s-light/lvds_4ch_link/driver/export/board_pdf/driver-F.SilkS.pdf

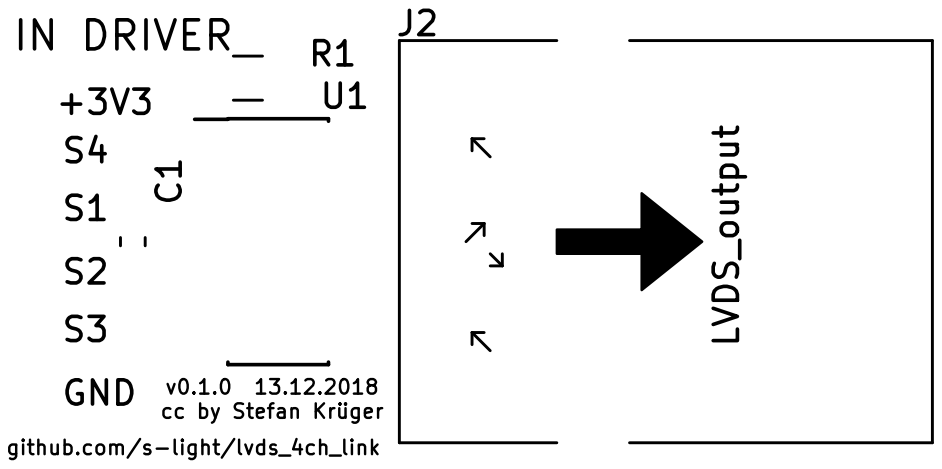
[picture p11: page 1]

cc by Stefan Krüger DRIVER
