s-light/lvds_4ch_link/receiver/export/board_pdf/receiver-B.Cu.pdf

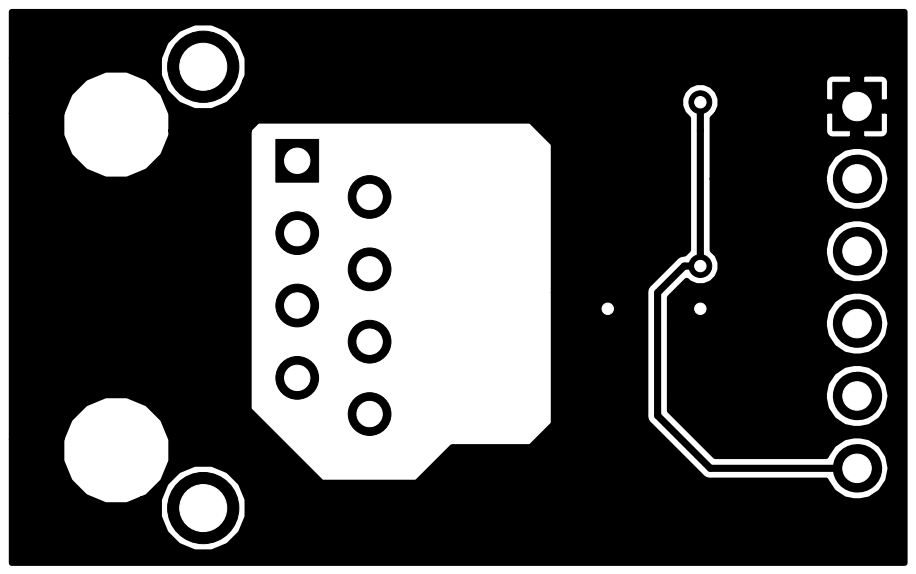
[picture p12: page 1]

Stefan Krüger CC BY Open Source Hardware

File: receiver.kicad_pcb Sheet: s-light.eu

Id: 1/1 Title: LVDS 4ch Driver
