s-light/lvds_4ch_link/receiver/export/board_pdf/receiver-F.SilkS.pdf

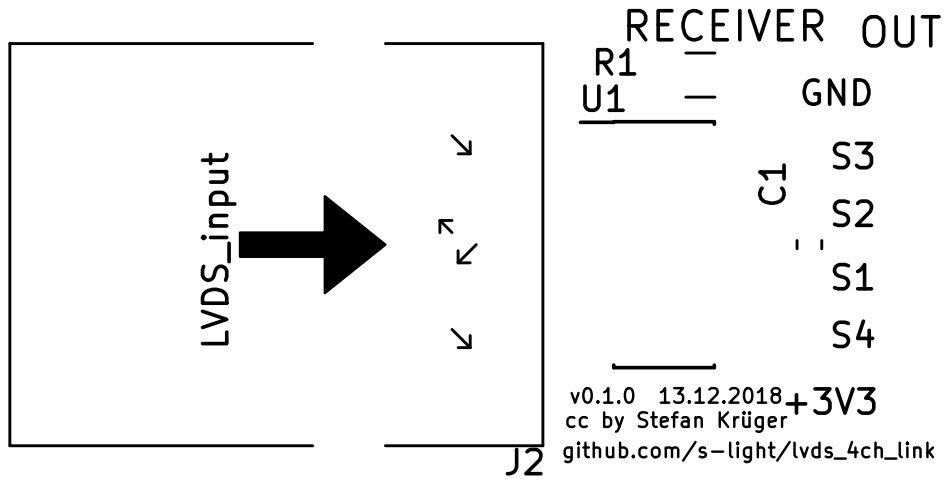
[picture p13: page 1]

cc by Stefan Krüger RECEIVER
S3S2S1 GND

Stefan Krüger CC BY Open Source Hardware

File: receiver.kicad_pcb Sheet: s-light.eu

Id: 1/1 Title: LVDS 4ch Driver
