s-light/lvds_4ch_link/driver/export/board_pdf/output.pdf

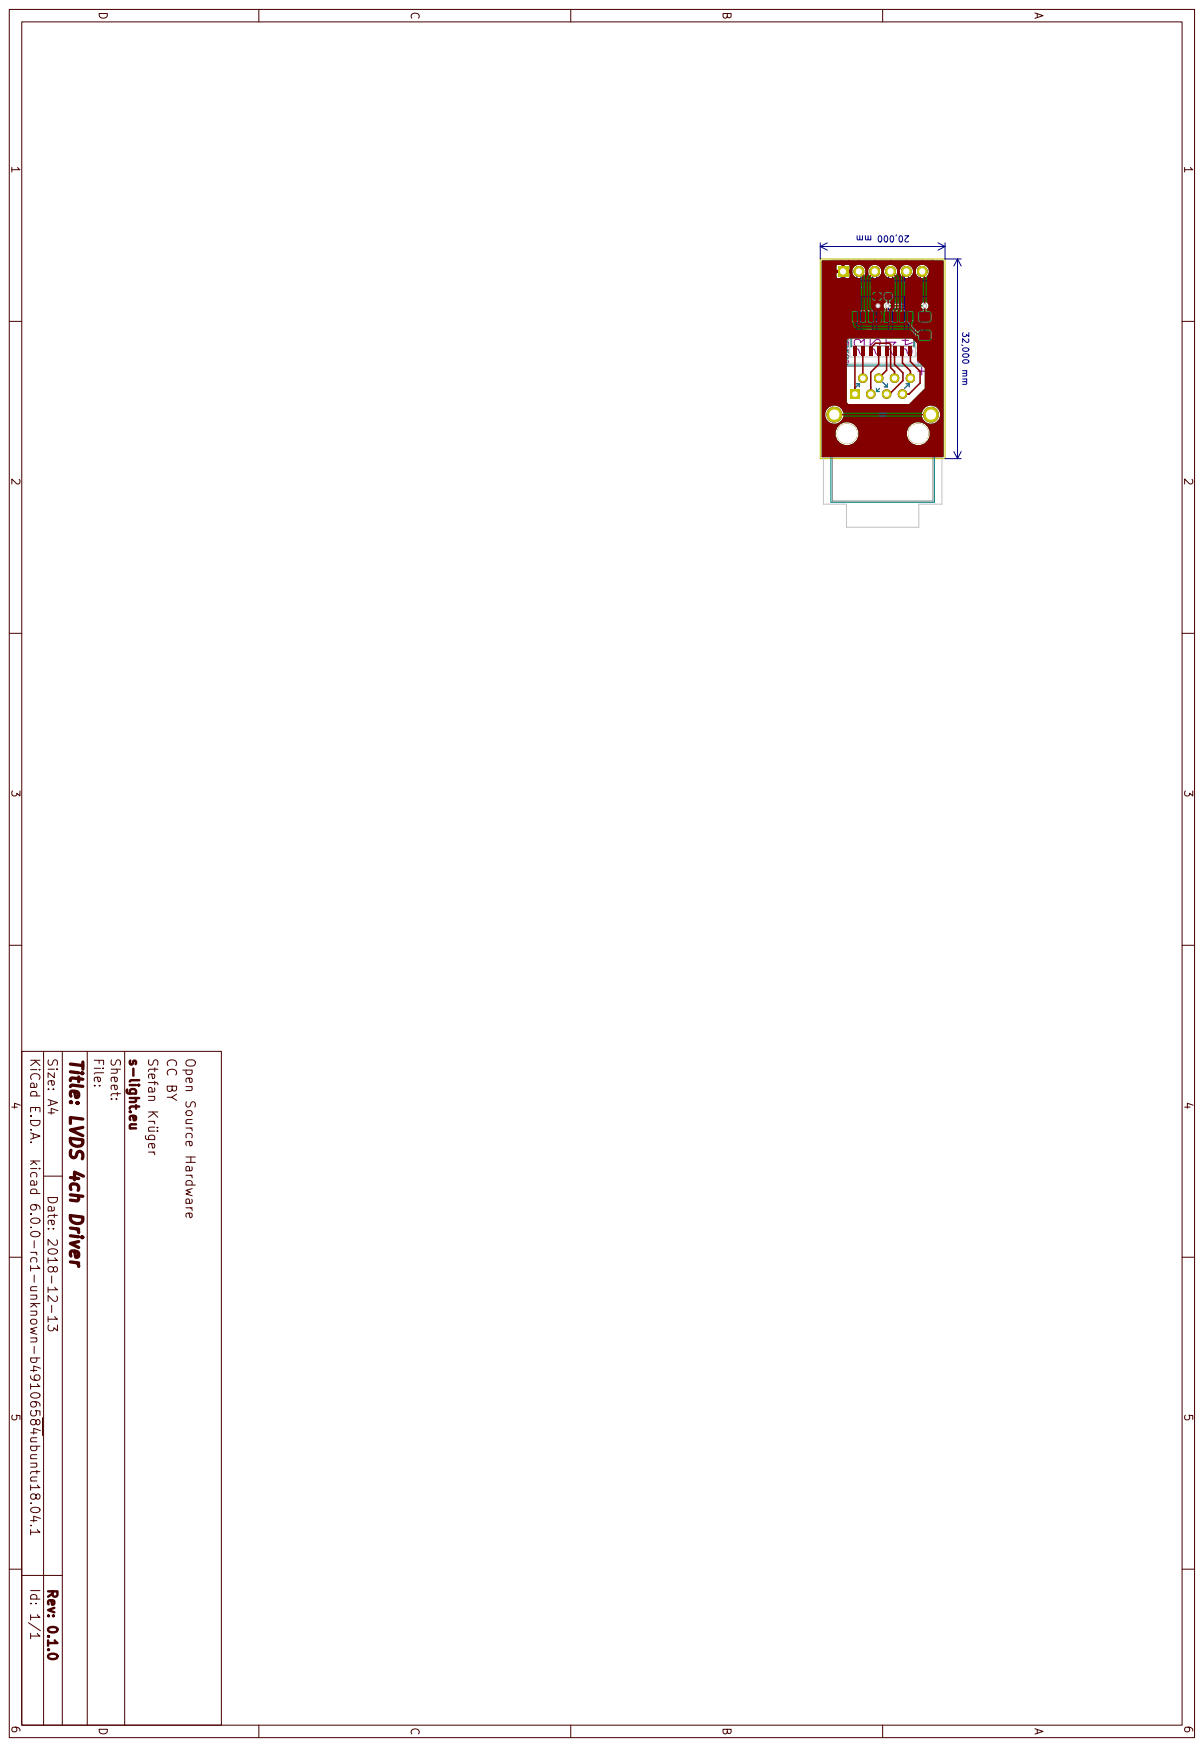
[picture p23: page 1]
