s-light/lvds_4ch_link/receiver/export/board_pdf/output.pdf

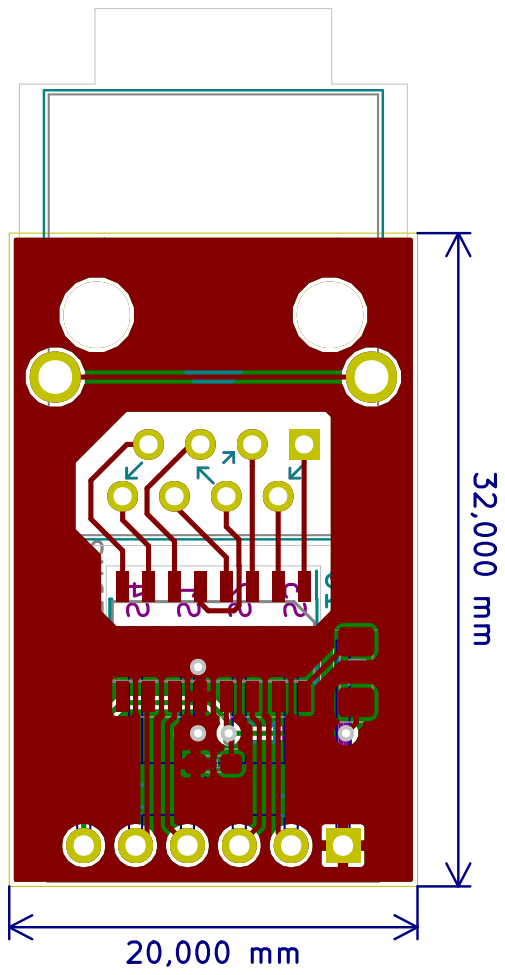
[picture p24: page 1]
